ingobecker/pcb-bakery/src/src/bluepill.c

#include <libopencm3/stm32/gpio.h>
#include <libopencm3/stm32/rcc.h>
#include <libopencm3/stm32/usart.h>
#include "bluepill.h"

void bluepill_led_setup()
{
	rcc_periph_clock_enable(BLUEPILL_LED_RCC_BIT);
	gpio_set_mode(BLUEPILL_LED_PORT, GPIO_MODE_OUTPUT_2_MHZ,
		GPIO_CNF_OUTPUT_PUSHPULL, BLUEPILL_LED_PIN);
}

void bluepill_uart_setup()
{
	rcc_periph_clock_enable(RCC_GPIOA);
	rcc_periph_clock_enable(RCC_AFIO);
	rcc_periph_clock_enable(RCC_USART1);
	gpio_set_mode(GPIOA, GPIO_MODE_OUTPUT_50_MHZ,
		GPIO_CNF_OUTPUT_ALTFN_PUSHPULL, GPIO_USART1_TX);

	/* Setup UART parameters. */
	usart_set_baudrate(USART1, 115200);
	usart_set_databits(USART1, 8);
	usart_set_stopbits(USART1, USART_STOPBITS_1);
	usart_set_parity(USART1, USART_PARITY_NONE);
	usart_set_flow_control(USART1, USART_FLOWCONTROL_NONE);
	usart_set_mode(USART1, USART_MODE_TX);

	/* Finally enable the USART. */
	usart_enable(USART1);
}
